Mokeded/Symm60HE/plate/Symm60HE-plate-universal-right.dxf

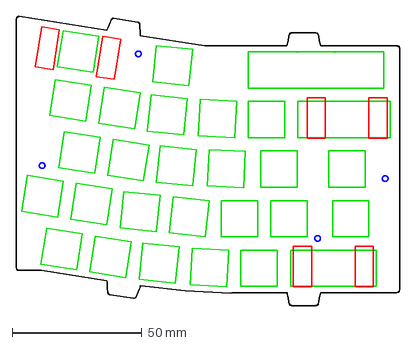
[picture p15: CAD file, 2026-10-05]
plate/Symm60HE-plate-universal-right.dxf
147.4 x 111.2 mm
