Mokeded/Symm60HE/case/fusion360/models/official/CCTC_TCC0603X5R106M6R3CT_C380318.step

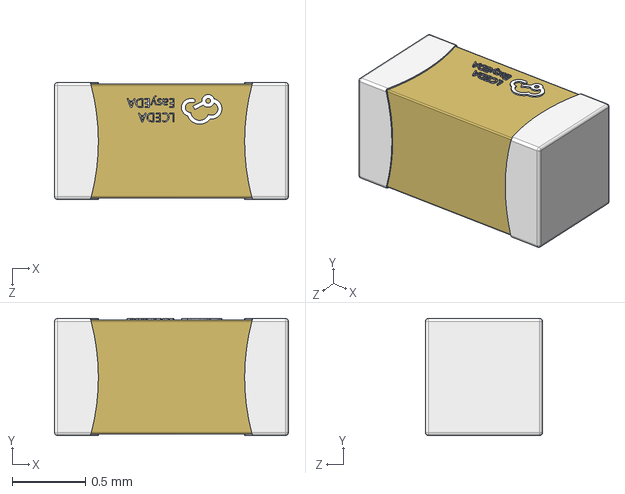
[picture p16: CAD file, 2026-10-05]
case/fusion360/models/official/CCTC_TCC0603X5R106M6R3CT_C380318.step
1.60 x 0.8 x 0.8 mm
