Mokeded/Symm60HE/case/fusion360/Symm60HE-RightPlate.step

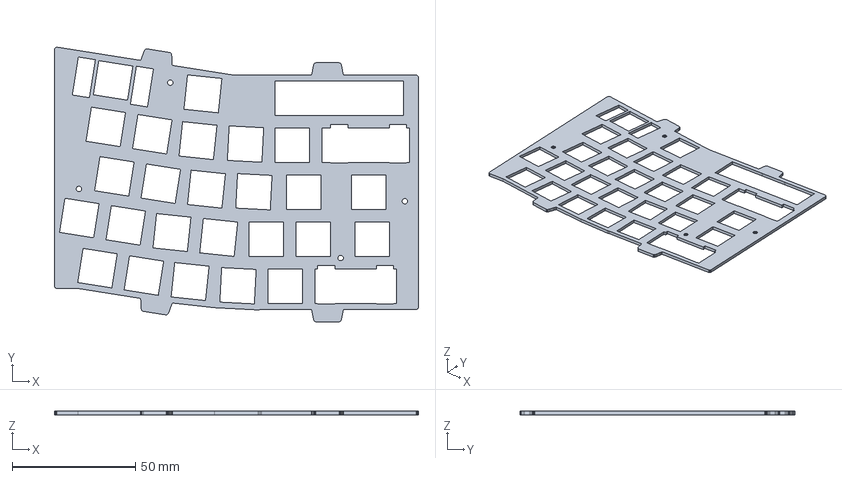
[picture p17: CAD file, 2026-10-05]
case/fusion360/Symm60HE-RightPlate.step
147.4 x 111.2 x 1.50 mm
