Mokeded/Symm60HE/plate/Symm60HE-plate-wkl-left-arrows-right-bs2-left.dxf

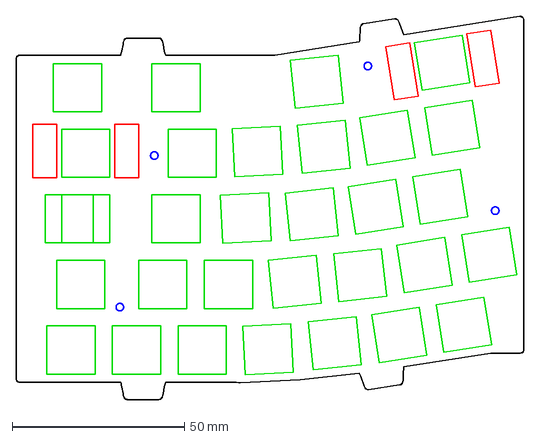
[picture p18: CAD file, 2026-10-05]
plate/Symm60HE-plate-wkl-left-arrows-right-bs2-left.dxf
147.4 x 111.2 mm
