Mokeded/Symm60HE/case/fusion360/models/official/TI_SN74AHCT1G125DBVR_C7484.step

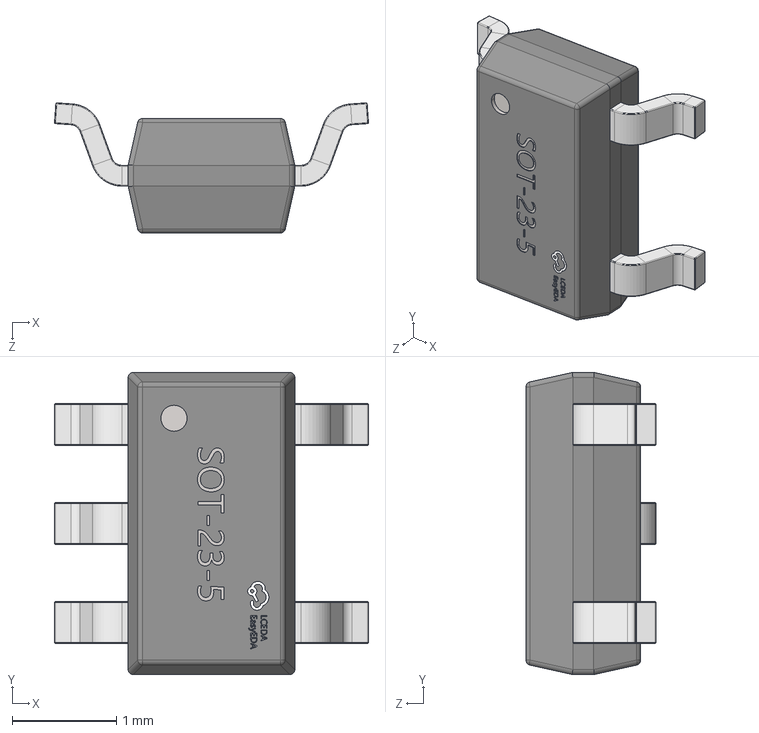
[picture p19: CAD file, 2026-10-05]
case/fusion360/models/official/TI_SN74AHCT1G125DBVR_C7484.step
3.01 x 2.90 x 1.25 mm
