Mokeded/Symm60HE/case/fusion360/Symm60HE-LeftRibbonCable.step

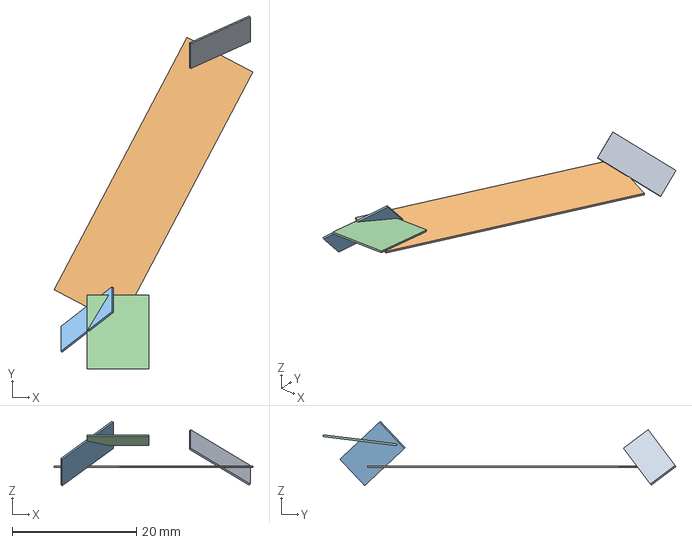
[picture p20: CAD file, 2026-10-05]
case/fusion360/Symm60HE-LeftRibbonCable.step
32.0 x 56.8 x 10.4 mm
