Mokeded/Symm60HE/case/fusion360/models/official/OPSCO_SK6812MINI-E_C5149201.step

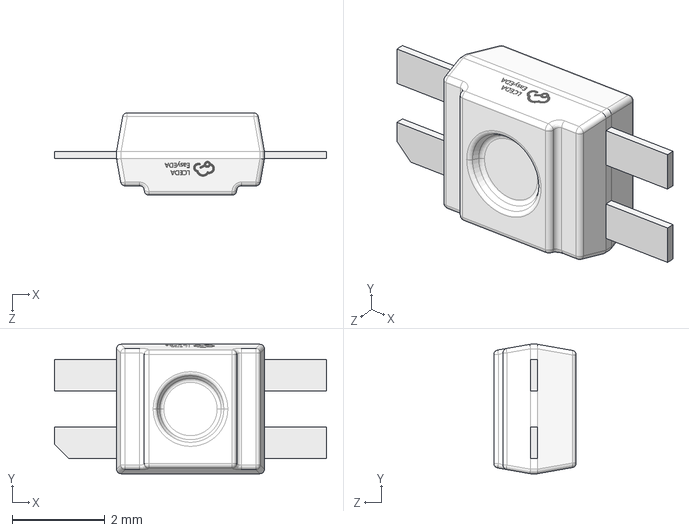
[picture p22: CAD file, 2026-10-05]
case/fusion360/models/official/OPSCO_SK6812MINI-E_C5149201.step
5.88 x 2.80 x 1.78 mm
