Mokeded/Symm60HE/case/fusion360/Symm60HE-LeftPlate.step

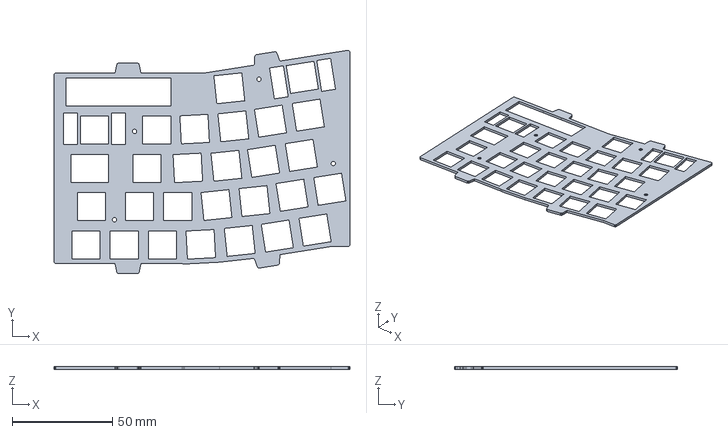
[picture p23: CAD file, 2026-10-05]
case/fusion360/Symm60HE-LeftPlate.step
147.4 x 111.2 x 1.50 mm
