Mokeded/Symm60HE/plate/Symm60HE-gasket-pads-wklarrows.dxf

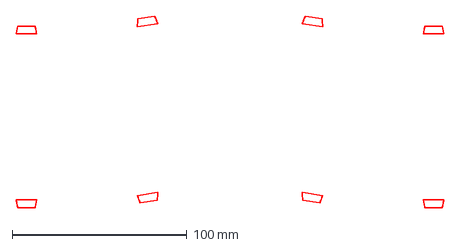
[picture p24: CAD file, 2026-10-05]
plate/Symm60HE-gasket-pads-wklarrows.dxf
244.8 x 109.5 mm
