Mokeded/Symm60HE/case/fusion360/models/official/ARTERY_AT32F405RCT7_C47090415.step

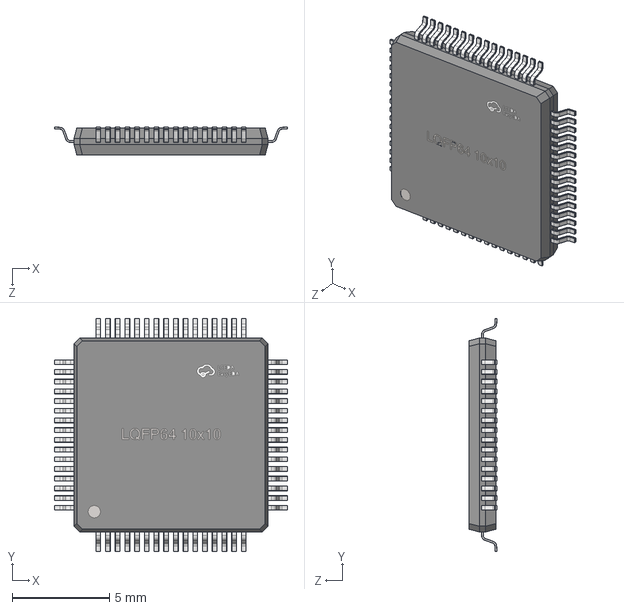
[picture p25: CAD file, 2026-10-05]
case/fusion360/models/official/ARTERY_AT32F405RCT7_C47090415.step
12.0 x 12.0 x 1.45 mm
