Mokeded/Symm60HE/plate/Symm60HE-gasket-pads-three-key-left-wkl-right.dxf

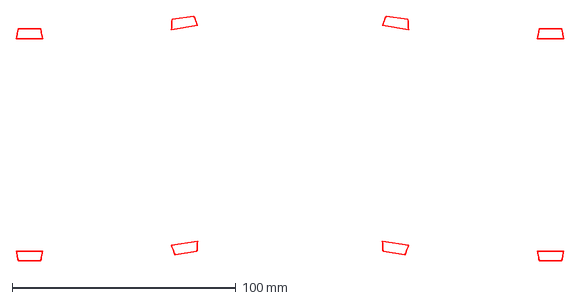
[picture p26: CAD file, 2026-10-05]
plate/Symm60HE-gasket-pads-three-key-left-wkl-right.dxf
244.8 x 109.5 mm
