Mokeded/Symm60HE/case/fusion360/models/official/UNI-ROYAL_0402WGF1202TCE_C25752.step

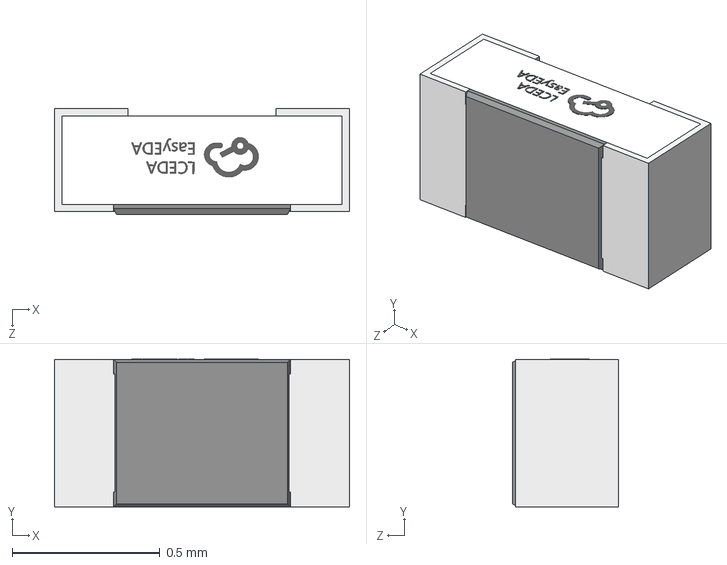
[picture p27: CAD file, 2026-10-05]
case/fusion360/models/official/UNI-ROYAL_0402WGF1202TCE_C25752.step
1.00 x 0.501 x 0.36 mm
