Mokeded/Symm60HE/case/fusion360/Symm60HE-RightSwitches.step

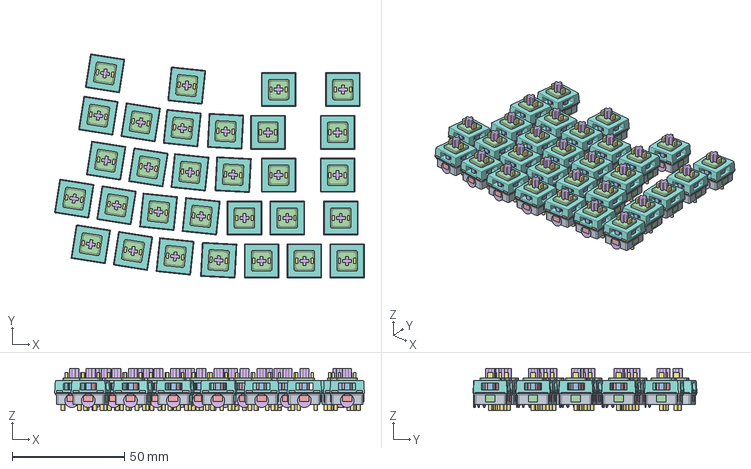
[picture p28: CAD file, 2026-10-05]
case/fusion360/Symm60HE-RightSwitches.step
137.9 x 99.8 x 18.8 mm
