Mokeded/Symm60HE/case/fusion360/models/official/TI_SN74LV4051APWR_C7793.step

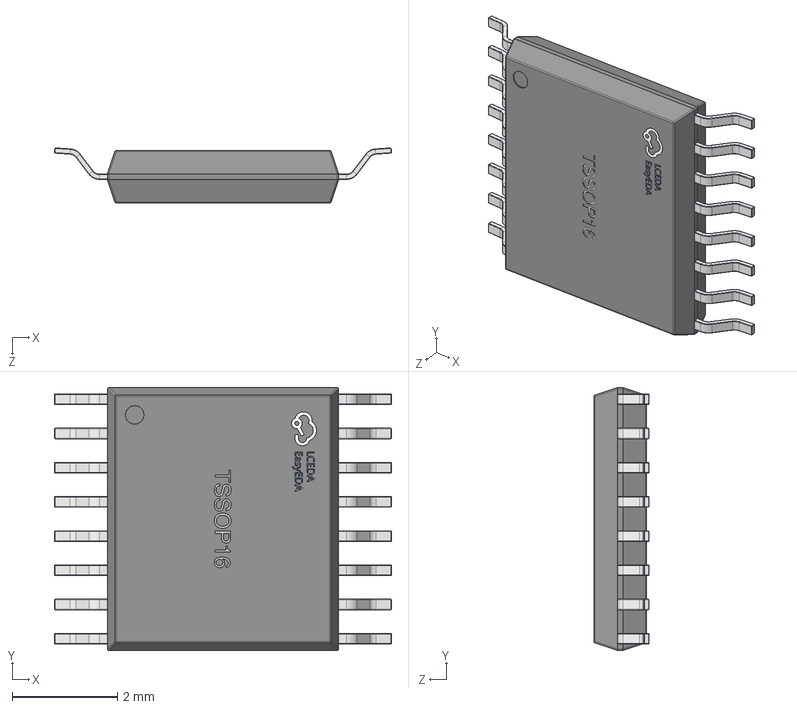
[picture p30: CAD file, 2026-10-05]
case/fusion360/models/official/TI_SN74LV4051APWR_C7793.step
6.41 x 5.00 x 1.05 mm
