Mokeded/Symm60HE/case/fusion360/Symm60HE-RightRibbonCable.step

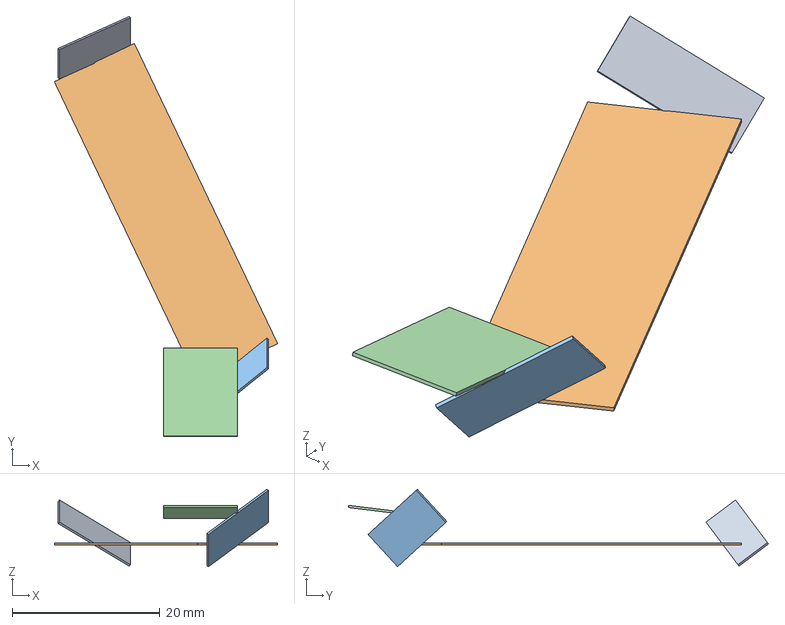
[picture p31: CAD file, 2026-10-05]
case/fusion360/Symm60HE-RightRibbonCable.step
30.2 x 56.8 x 10.5 mm
