Mokeded/Symm60HE/case/fusion360/models/official/YXC_X322512MSB4SI_C9002.step

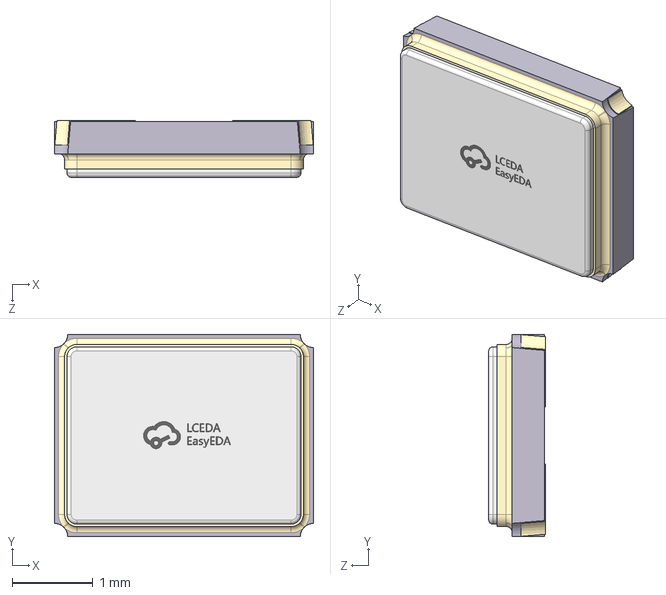
[picture p33: CAD file, 2026-10-05]
case/fusion360/models/official/YXC_X322512MSB4SI_C9002.step
3.20 x 2.50 x 0.701 mm
