Mokeded/Symm60HE/plate/Symm60HE-plate-wklbs2-left.dxf

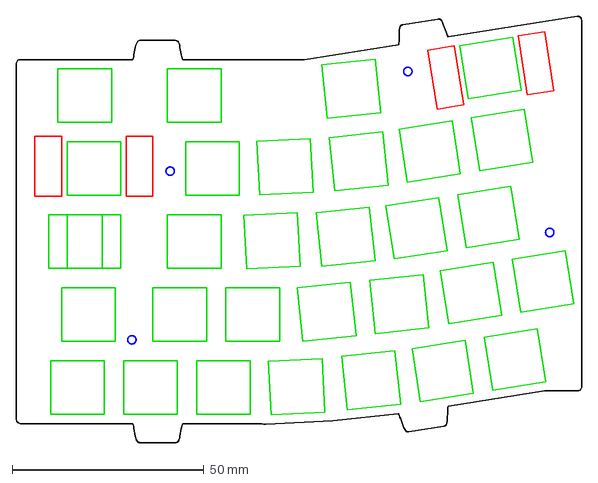
[picture p34: CAD file, 2026-10-05]
plate/Symm60HE-plate-wklbs2-left.dxf
147.4 x 111.2 mm
