Mokeded/Symm60HE/case/fusion360/models/official/NOVOSENSE_MT9102ET_C5447698.step

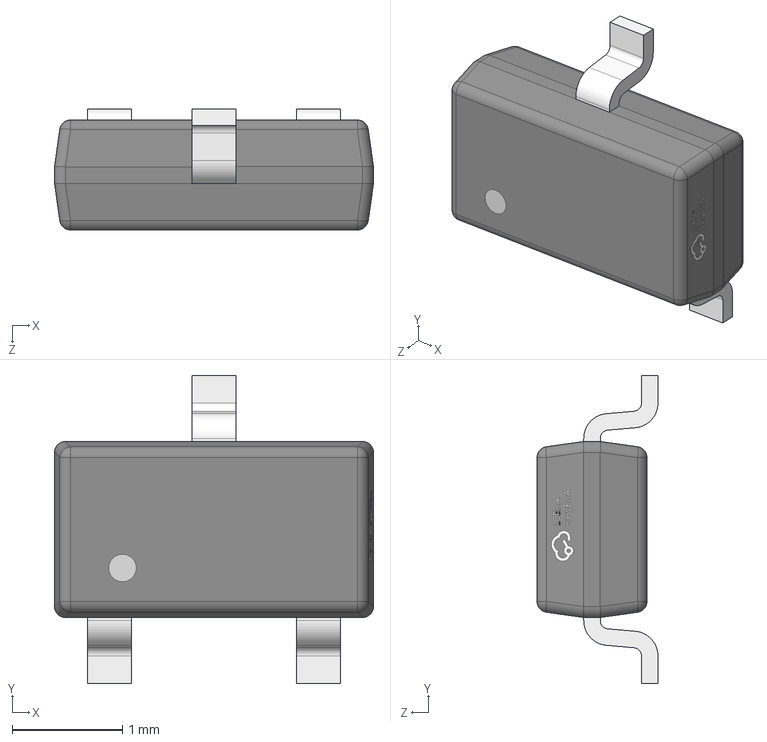
[picture p35: CAD file, 2026-10-05]
case/fusion360/models/official/NOVOSENSE_MT9102ET_C5447698.step
2.90 x 2.80 x 1.10 mm
