Mokeded/Symm60HE/case/fusion360/models/official/XKB_TS-1187A-B-A-B_C318884.stp

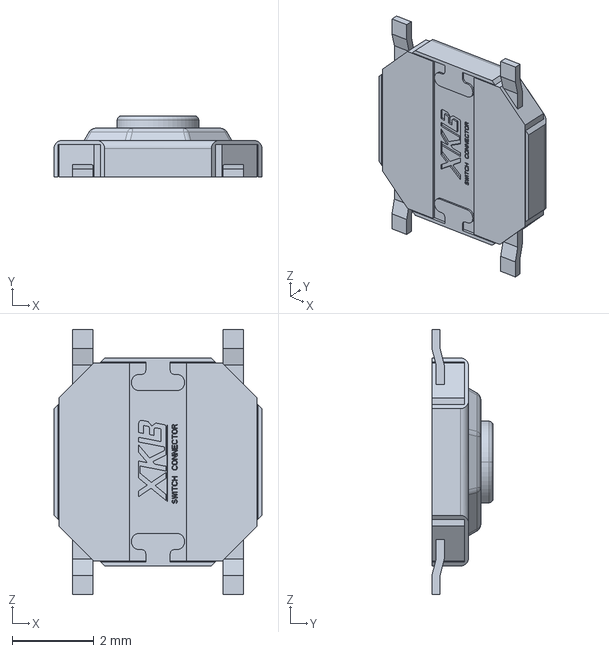
[picture p37: CAD file, 2026-09-21]
case/fusion360/models/official/XKB_TS-1187A-B-A-B_C318884.stp
5.10 x 1.50 x 6.50 mm
