Mokeded/Symm60HE/plate/Symm60HE-plate-wklarrows-left.dxf

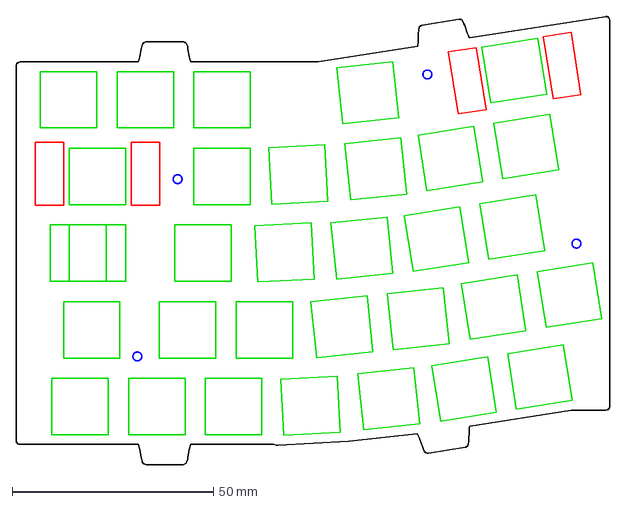
[picture p38: CAD file, 2026-10-05]
plate/Symm60HE-plate-wklarrows-left.dxf
147.4 x 111.2 mm
