Mokeded/Symm60HE/case/fusion360/models/official/BOOMELE_1.0-12P_C20111.step

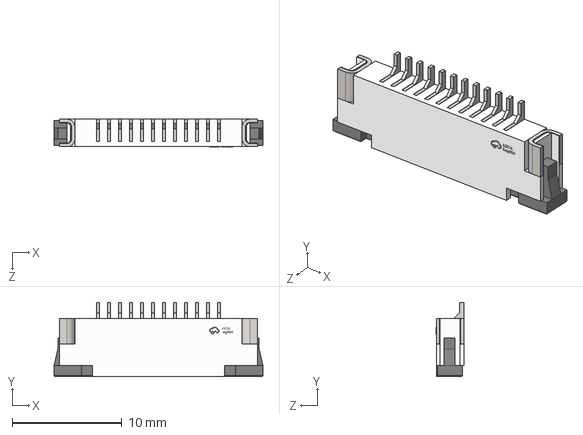
[picture p39: CAD file, 2026-09-13]
case/fusion360/models/official/BOOMELE_1.0-12P_C20111.step
19.0 x 6.75 x 2.51 mm
