Mokeded/Symm60HE/case/fusion360/Symm60HE-DaughterboardPCBComponents.step

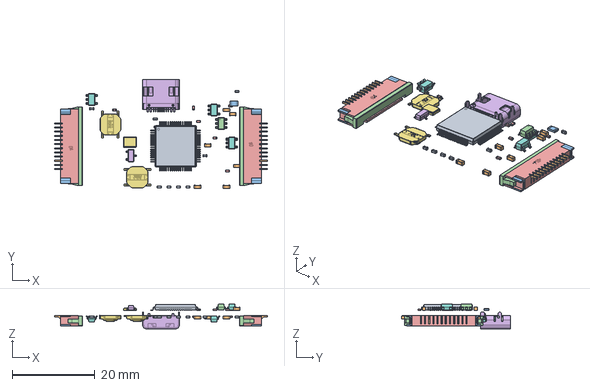
[picture p40: CAD file, 2026-09-21]
case/fusion360/Symm60HE-DaughterboardPCBComponents.step
51.3 x 26.3 x 6.00 mm
