Mokeded/Symm60HE/case/fusion360/models/official/HRO_TYPE-C-31-M-12_C165948.step

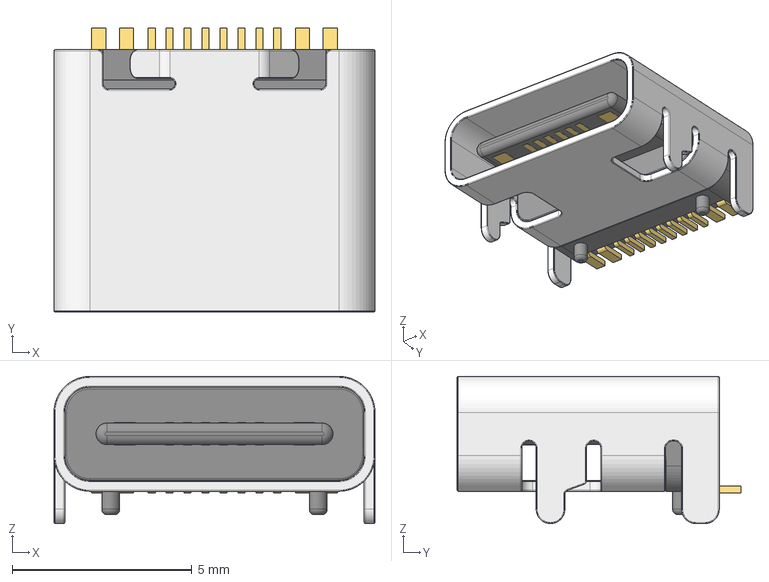
[picture p42: CAD file, 2026-09-13]
case/fusion360/models/official/HRO_TYPE-C-31-M-12_C165948.step
8.94 x 7.90 x 4.10 mm
