Mokeded/Symm60HE/plate/Symm60HE-plate-wklarrows-right.dxf

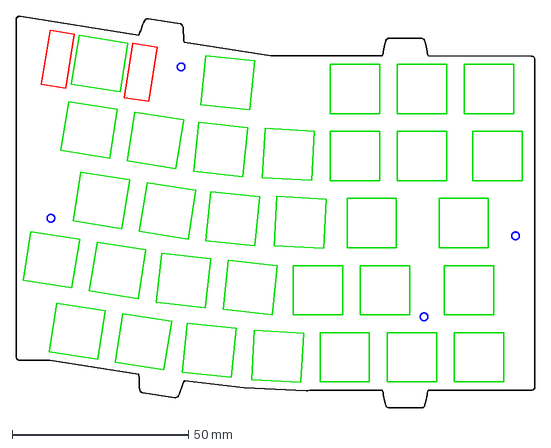
[picture p44: CAD file, 2026-10-05]
plate/Symm60HE-plate-wklarrows-right.dxf
147.4 x 111.2 mm
