Mokeded/Symm60HE/plate/Symm60HE-gasket-pads-universal.dxf

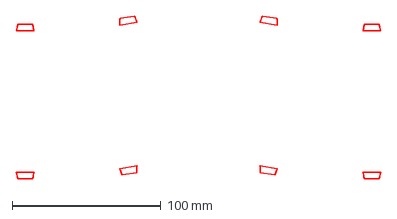
[picture p45: CAD file, 2026-10-05]
plate/Symm60HE-gasket-pads-universal.dxf
244.8 x 109.5 mm
