Mokeded/Symm60HE/plate/Symm60HE-plate-universal-left.dxf

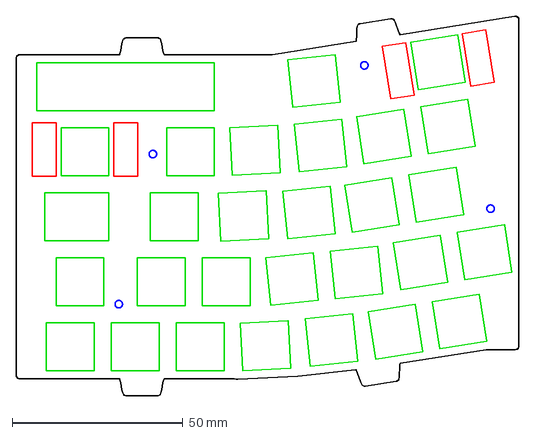
[picture p46: CAD file, 2026-10-05]
plate/Symm60HE-plate-universal-left.dxf
147.4 x 111.2 mm
