Mokeded/Symm60HE/plate/Symm60HE-gasket-pads-wklbs2.dxf

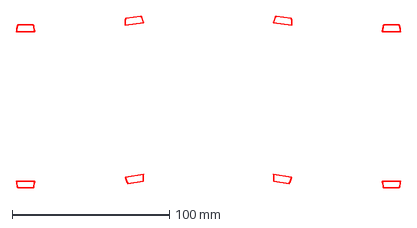
[picture p47: CAD file, 2026-10-05]
plate/Symm60HE-gasket-pads-wklbs2.dxf
244.8 x 109.5 mm
