Mokeded/Symm60HE/plate/Symm60HE-plate-wkl-left-arrows-right-right.dxf

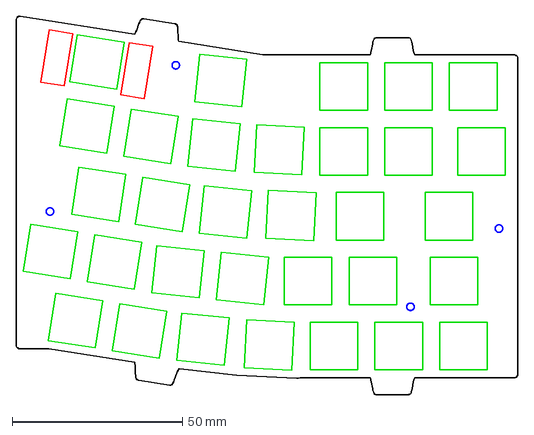
[picture p48: CAD file, 2026-10-05]
plate/Symm60HE-plate-wkl-left-arrows-right-right.dxf
147.4 x 111.2 mm
