Mokeded/Symm60HE/plate/Symm60HE-gasket-pads-wkl-left-arrows-right.dxf

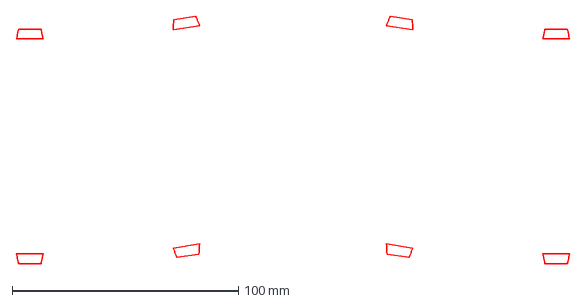
[picture p49: CAD file, 2026-10-05]
plate/Symm60HE-gasket-pads-wkl-left-arrows-right.dxf
244.8 x 109.5 mm
