Mokeded/Symm60HE/plate/Symm60HE-plate-wklbs2arrows-right.dxf

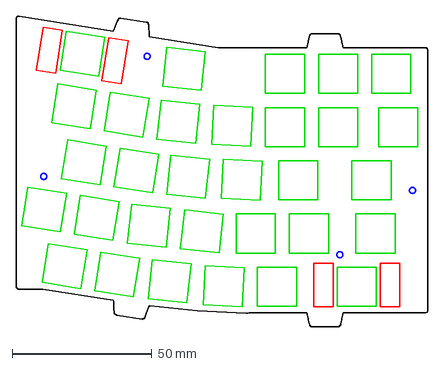
[picture p50: CAD file, 2026-10-05]
plate/Symm60HE-plate-wklbs2arrows-right.dxf
147.4 x 111.2 mm
