Mokeded/Symm60HE/plate/Symm60HE-plate-wkl-left-arrows-right-left.dxf

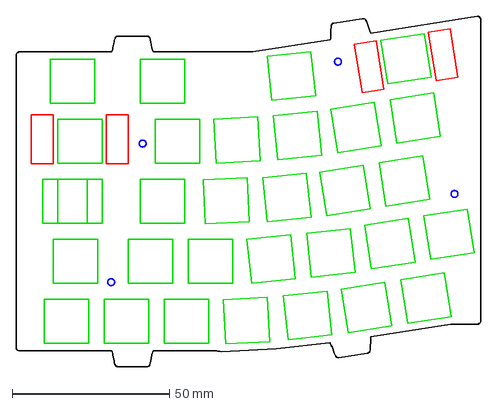
[picture p51: CAD file, 2026-10-05]
plate/Symm60HE-plate-wkl-left-arrows-right-left.dxf
147.4 x 111.2 mm
