Mokeded/Symm60HE/plate/Symm60HE-plate-three-key-left-wkl-right-left.dxf

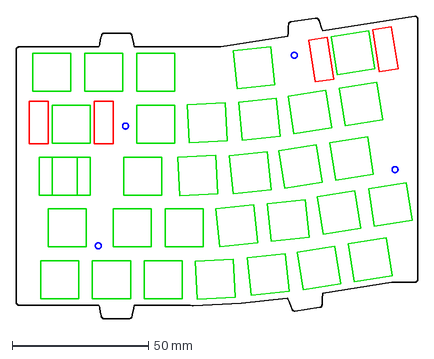
[picture p52: CAD file, 2026-10-05]
plate/Symm60HE-plate-three-key-left-wkl-right-left.dxf
147.4 x 111.2 mm
