Mokeded/Symm60HE/plate/Symm60HE-plate-wklbs2-right.dxf

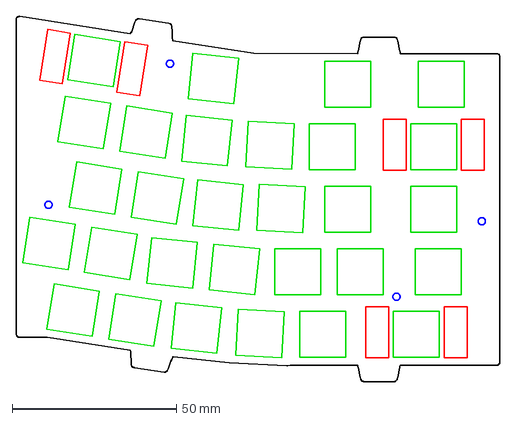
[picture p54: CAD file, 2026-10-05]
plate/Symm60HE-plate-wklbs2-right.dxf
147.4 x 111.2 mm
