Mokeded/Symm60HE/plate/Symm60HE-gasket-pads-wkl-left-arrows-right-bs2.dxf

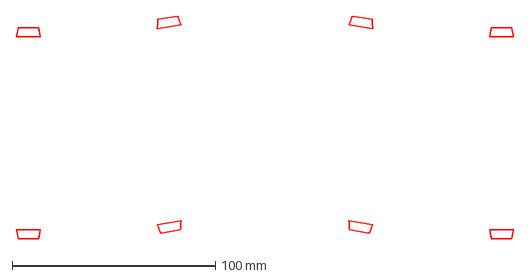
[picture p55: CAD file, 2026-10-05]
plate/Symm60HE-gasket-pads-wkl-left-arrows-right-bs2.dxf
244.8 x 109.5 mm
