Mokeded/Symm60HE/plate/Symm60HE-plate-wkl-right.dxf

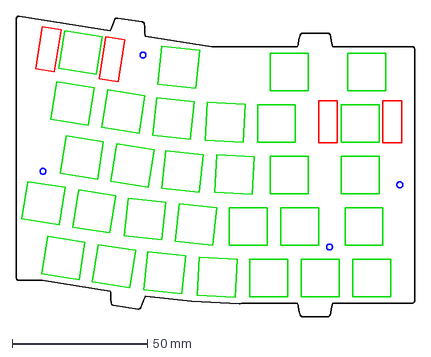
[picture p56: CAD file, 2026-10-05]
plate/Symm60HE-plate-wkl-right.dxf
147.4 x 111.2 mm
