Mokeded/Symm60HE/plate/DOE60-plate-wklbs2arrows.dxf

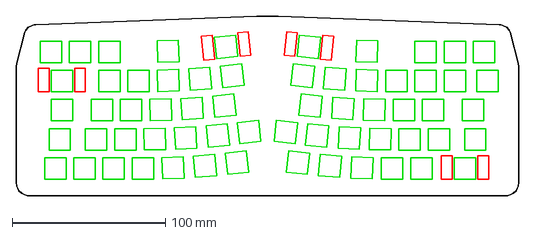
[picture p57: CAD file, 2026-09-10]
plate/DOE60-plate-wklbs2arrows.dxf
328.0 x 117.2 mm
