Mokeded/Symm60HE/plate/DOE60-plate-wklbs2.dxf

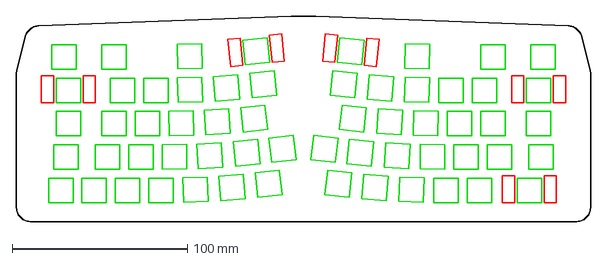
[picture p58: CAD file, 2026-09-10]
plate/DOE60-plate-wklbs2.dxf
328.0 x 117.2 mm
