Mokeded/Symm60HE/plate/DOE60-plate-universal.dxf

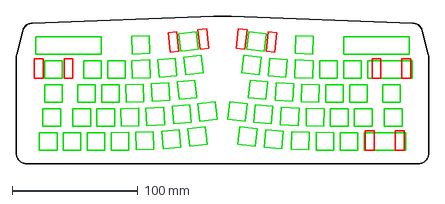
[picture p59: CAD file, 2026-09-10]
plate/DOE60-plate-universal.dxf
328.0 x 117.2 mm
