Mokeded/Symm60HE/plate/DOE60-plate-wkl.dxf

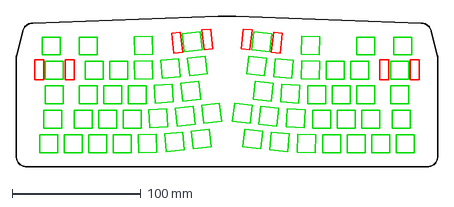
[picture p60: CAD file, 2026-09-10]
plate/DOE60-plate-wkl.dxf
328.0 x 117.2 mm
