Mokeded/Symm60HE/plate/DOE60-plate-wklarrows.dxf

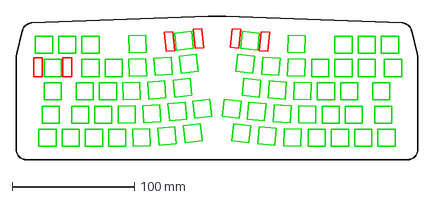
[picture p61: CAD file, 2026-09-10]
plate/DOE60-plate-wklarrows.dxf
328.0 x 117.2 mm
