Mokeded/Symm60HE/firmware/libhmk/src/migration.c

/*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
 * You should have received a copy of the GNU General Public License along with
 * this program. If not, see <https://www.gnu.org/licenses/>.
 */

#include "migration.h"

#include "eeconfig.h"
#include "wear_leveling.h"

#define MIGRATION_V1_0_GLOBAL_CONFIG_SIZE 12
#define MIGRATION_V1_0_ADVANCED_KEY_SIZE 12
#define MIGRATION_V1_0_PROFILE_CONFIG_SIZE                                     \
  (NUM_LAYERS * NUM_KEYS + NUM_KEYS * 4 +                                      \
   NUM_ADVANCED_KEYS * MIGRATION_V1_0_ADVANCED_KEY_SIZE + 1)

static bool v1_1_global_config_func(uint8_t *dst, const uint8_t *src);
static bool v1_1_profile_config_func(uint8_t profile, uint8_t *dst,
                                     const uint8_t *src);

#define MIGRATION_V1_1_GLOBAL_CONFIG_SIZE 14
#define MIGRATION_V1_1_PROFILE_CONFIG_SIZE                                     \
  (NUM_LAYERS * NUM_KEYS + NUM_KEYS * 4 +                                      \
   NUM_ADVANCED_KEYS * MIGRATION_V1_0_ADVANCED_KEY_SIZE + NUM_KEYS + 9 + 1)

static bool v1_2_global_config_func(uint8_t *dst, const uint8_t *src);
static bool v1_2_profile_config_func(uint8_t profile, uint8_t *dst,
                                     const uint8_t *src);

#define MIGRATION_V1_2_GLOBAL_CONFIG_SIZE (14 + NUM_KEYS * 2)
#define MIGRATION_V1_2_PROFILE_CONFIG_SIZE MIGRATION_V1_1_PROFILE_CONFIG_SIZE

static bool v1_3_global_config_func(uint8_t *dst, const uint8_t *src);
static bool v1_3_profile_config_func(uint8_t profile, uint8_t *dst,
                                     const uint8_t *src);

#define MIGRATION_V1_3_GLOBAL_CONFIG_SIZE MIGRATION_V1_2_GLOBAL_CONFIG_SIZE
#define MIGRATION_V1_3_PROFILE_CONFIG_SIZE MIGRATION_V1_2_PROFILE_CONFIG_SIZE

static bool v1_4_global_config_func(uint8_t *dst, const uint8_t *src);
static bool v1_4_profile_config_func(uint8_t profile, uint8_t *dst,
                                     const uint8_t *src);

#define MIGRATION_V1_4_GLOBAL_CONFIG_SIZE MIGRATION_V1_3_GLOBAL_CONFIG_SIZE
#define MIGRATION_V1_4_PROFILE_CONFIG_SIZE MIGRATION_V1_3_PROFILE_CONFIG_SIZE

static bool v1_5_global_config_func(uint8_t *dst, const uint8_t *src);
static bool v1_5_profile_config_func(uint8_t profile, uint8_t *dst,
                                     const uint8_t *src);

#define MIGRATION_V1_5_GLOBAL_CONFIG_SIZE MIGRATION_V1_4_GLOBAL_CONFIG_SIZE
#define MIGRATION_V1_5_ADVANCED_KEY_SIZE                                       \
  (3 + 2 * NUM_DYNAMIC_KEYSTROKE_MAX_BINDINGS + 1)
#define MIGRATION_V1_5_MACRO_NODE_SIZE 4
#define MIGRATION_V1_5_MACRO_NODE_NONE UINT8_MAX
#define MIGRATION_V1_5_PROFILE_CONFIG_SIZE                                     \
  (NUM_LAYERS * NUM_KEYS + NUM_KEYS * 4 +                                      \
   NUM_ADVANCED_KEYS * MIGRATION_V1_5_ADVANCED_KEY_SIZE +                      \
   NUM_MACRO_NODES * MIGRATION_V1_5_MACRO_NODE_SIZE + NUM_KEYS + 9 + 1)

#if defined(RGB_ENABLE)
static bool v1_6_global_config_func(uint8_t *dst, const uint8_t *src);
static bool v1_6_profile_config_func(uint8_t profile, uint8_t *dst,
                                     const uint8_t *src);

#define MIGRATION_V1_6_GLOBAL_CONFIG_SIZE                                      \
  (MIGRATION_V1_5_GLOBAL_CONFIG_SIZE + sizeof(rgb_config_t))
#define MIGRATION_V1_6_PROFILE_CONFIG_SIZE MIGRATION_V1_5_PROFILE_CONFIG_SIZE
#endif

// Migration metadata for each configuration version. The first entry is
// reserved for the initial version (v1.0) which does not require migration.
static const migration_t migrations[] = {
    {
        .version = 0x0100,
        .global_config_size = MIGRATION_V1_0_GLOBAL_CONFIG_SIZE,
        .profile_config_size = MIGRATION_V1_0_PROFILE_CONFIG_SIZE,
    },
    {
        .version = 0x0101,
        .global_config_size = MIGRATION_V1_1_GLOBAL_CONFIG_SIZE,
        .profile_config_size = MIGRATION_V1_1_PROFILE_CONFIG_SIZE,
        .global_config_func = v1_1_global_config_func,
        .profile_config_func = v1_1_profile_config_func,
    },
    {
        .version = 0x0102,
        .global_config_size = MIGRATION_V1_2_GLOBAL_CONFIG_SIZE,
        .profile_config_size = MIGRATION_V1_2_PROFILE_CONFIG_SIZE,
        .global_config_func = v1_2_global_config_func,
        .profile_config_func = v1_2_profile_config_func,
    },
    {
        .version = 0x0103,
        .global_config_size = MIGRATION_V1_3_GLOBAL_CONFIG_SIZE,
        .profile_config_size = MIGRATION_V1_3_PROFILE_CONFIG_SIZE,
        .global_config_func = v1_3_global_config_func,
        .profile_config_func = v1_3_profile_config_func,
    },
    {
        .version = 0x0104,
        .global_config_size = MIGRATION_V1_4_GLOBAL_CONFIG_SIZE,
        .profile_config_size = MIGRATION_V1_4_PROFILE_CONFIG_SIZE,
        .global_config_func = v1_4_global_config_func,
        .profile_config_func = v1_4_profile_config_func,
    },
    {
        .version = 0x0105,
        .global_config_size = MIGRATION_V1_5_GLOBAL_CONFIG_SIZE,
        .profile_config_size = MIGRATION_V1_5_PROFILE_CONFIG_SIZE,
        .global_config_func = v1_5_global_config_func,
        .profile_config_func = v1_5_profile_config_func,
    },
#if defined(RGB_ENABLE)
    {
        .version = 0x0106,
        .global_config_size = MIGRATION_V1_6_GLOBAL_CONFIG_SIZE,
        .profile_config_size = MIGRATION_V1_6_PROFILE_CONFIG_SIZE,
        .global_config_func = v1_6_global_config_func,
        .profile_config_func = v1_6_profile_config_func,
    },
#endif
};

// An assertion to remind us to bump the persistent configuration version, and
// implement a migration function if there is a change to the configuration
// type. Update the assertion when a new version is added.
#if defined(RGB_ENABLE)
_Static_assert(MIGRATION_V1_6_GLOBAL_CONFIG_SIZE +
                       NUM_PROFILES * MIGRATION_V1_6_PROFILE_CONFIG_SIZE ==
                   offsetof(eeconfig_t, magic_end),
               "Invalid RGB configuration size");
#else
_Static_assert(MIGRATION_V1_5_GLOBAL_CONFIG_SIZE +
                       NUM_PROFILES * MIGRATION_V1_5_PROFILE_CONFIG_SIZE ==
                   offsetof(eeconfig_t, magic_end),
               "Invalid configuration size");
#endif

// An assertion to remind us if there is a breaking change to `MACRO_NODE_NONE`.
// Update the assertion when a new version is added.
_Static_assert(MIGRATION_V1_5_MACRO_NODE_NONE == MACRO_NODE_NONE,
               "Invalid MACRO_NODE_NONE");

bool migration_try_migrate(void) {
  if (eeconfig->magic_start != EECONFIG_MAGIC_START)
    // The magic start is always the same for any version.
    return false;

  const uint16_t config_version = eeconfig->version;
  // We alternate between two buffers to save the memory.
  uint8_t current_buf = 0;
  uint8_t bufs[2][sizeof(eeconfig_t)];

  // Let `bufs[0]` be the current configuration.
  memcpy(bufs[0], eeconfig, sizeof(eeconfig_t));
  // Skip v1.0 migration since it is the initial version
  for (uint32_t i = 1; i < M_ARRAY_SIZE(migrations); i++) {
    const migration_t *m = &migrations[i];
    const migration_t *prev_m = &migrations[i - 1];

    if (m->version <= config_version)
      // Skip migrations that are not applicable
      continue;

    const uint8_t *src = bufs[current_buf];
    uint8_t *dst = bufs[current_buf ^ 1];

    if (m->global_config_func && !m->global_config_func(dst, src))
      // Migration failed for the global configuration
      return false;

    if (m->profile_config_func) {
      for (uint8_t p = 0; p < NUM_PROFILES; p++) {
        // Move the pointers to the start of each profile configuration
        const uint8_t *profile_src =
            src + prev_m->global_config_size + p * prev_m->profile_config_size;
        uint8_t *profile_dst =
            dst + m->global_config_size + p * m->profile_config_size;

        if (!m->profile_config_func(p, profile_dst, profile_src))
          // Migration failed for the profile configuration
          return false;
      }
    }

    // Update the version in the destination buffer
    ((eeconfig_t *)dst)->version = m->version;
    // Switch to the next buffer for the next migration
    current_buf ^= 1;
  }

  // Make sure the configuration is valid after migration
  ((eeconfig_t *)bufs[current_buf])->magic_end = EECONFIG_MAGIC_END;
  // We reflect the update in the flash.
  return wear_leveling_write(0, &bufs[current_buf], sizeof(eeconfig_t));
}

//--------------------------------------------------------------------+
// Helper Functions
//--------------------------------------------------------------------+

static void migration_memcpy(uint8_t **dst, const uint8_t **src, uint32_t len) {
  memcpy(*dst, *src, len);
  *dst += len;
  *src += len;
}

static void migration_memset(uint8_t **dst, uint8_t value, uint32_t len) {
  memset(*dst, value, len);
  *dst += len;
}

#define MAKE_MIGRATION_ASSIGN(type)                                            \
  static void migration_assign_##type(uint8_t **dst, type value) {             \
    *(type *)(*dst) = value;                                                   \
    *dst = (uint8_t *)((type *)(*dst) + 1);                                    \
  }

MAKE_MIGRATION_ASSIGN(uint8_t)
MAKE_MIGRATION_ASSIGN(uint16_t)

//--------------------------------------------------------------------+
// v1.0 -> v1.1 Migration
//--------------------------------------------------------------------+

bool v1_1_global_config_func(uint8_t *dst, const uint8_t *src) {
  if (((eeconfig_t *)src)->version != 0x0100)
    // Expected version v1.0
    return false;

  // Copy `magic_start` to `calibration`
  migration_memcpy(&dst, &src, 10);
  // Default `options` to 0
  migration_assign_uint16_t(&dst, 0);
  // Copy `current_profile` and `last_non_default_profile`
  migration_memcpy(&dst, &src, 2);

  return true;
}

bool v1_1_profile_config_func(uint8_t profile, uint8_t *dst,
                              const uint8_t *src) {
  // Save the `keymap` offset
  uint8_t *keymap = dst;
  // Copy `keymap` to `actuation_map`
  migration_memcpy(&dst, &src, (NUM_LAYERS * NUM_KEYS) + (NUM_KEYS * 4));
  // Update keycodes to include `KC_INT1` ... `KC_LNG6`
  for (uint32_t i = 0; i < NUM_LAYERS * NUM_KEYS; i++) {
    if (0x70 <= keymap[i] && keymap[i] <= 0x71)
      // `KC_LNG1` and `KC_LNG2`
      keymap[i] += 0x06;
    else if (0x72 <= keymap[i] && keymap[i] <= 0x96)
      // `KC_LEFT_CTRL` ... `SP_MOUSE_BUTTON_5`
      keymap[i] += 0x09;
  }
  // Save the `advanced_keys` offset
  uint8_t *advanced_keys = dst;
  // Copy `advanced_keys`
  migration_memcpy(&dst, &src,
                   NUM_ADVANCED_KEYS * MIGRATION_V1_0_ADVANCED_KEY_SIZE);
  // Default `hold_on_other_key_press` to 0
  for (uint8_t i = 0; i < NUM_ADVANCED_KEYS; i++) {
    uint8_t *ak = advanced_keys + i * MIGRATION_V1_0_ADVANCED_KEY_SIZE;
    if (ak[2] == AK_TYPE_TAP_HOLD)
      ak[7] = 0;
  }
  // Set `gamepad_buttons` to 0
  migration_memset(&dst, 0, NUM_KEYS);
  // Default `analog_curve` to linear
  migration_assign_uint8_t(&dst, 4), migration_assign_uint8_t(&dst, 20);
  migration_assign_uint8_t(&dst, 85), migration_assign_uint8_t(&dst, 95);
  migration_assign_uint8_t(&dst, 165), migration_assign_uint8_t(&dst, 170);
  migration_assign_uint8_t(&dst, 255), migration_assign_uint8_t(&dst, 255);
  // Default `keyboard_enabled` and `snappy_joystick` to true
  migration_assign_uint8_t(&dst, 0b00001001);
  // Copy `tick_rate`
  migration_memcpy(&dst, &src, 1);

  return true;
}

//--------------------------------------------------------------------+
// v1.1 -> v1.2 Migration
//--------------------------------------------------------------------+

bool v1_2_global_config_func(uint8_t *dst, const uint8_t *src) {
  if (((eeconfig_t *)src)->version != 0x0101)
    // Expected version v1.1
    return false;

  // Copy `magic_start` to `calibration`
  migration_memcpy(&dst, &src, 10);
  // Set `bottom_out_threshold` to 0
  migration_memset(&dst, 0, NUM_KEYS * 2);
  // Copy `options` to `last_non_default_profile`
  migration_memcpy(&dst, &src, 4);

  return true;
}

bool v1_2_profile_config_func(uint8_t profile, uint8_t *dst,
                              const uint8_t *src) {
  // Copy the entire profile
  migration_memcpy(&dst, &src, MIGRATION_V1_2_PROFILE_CONFIG_SIZE);

  return true;
}

//--------------------------------------------------------------------+
// v1.2 -> v1.3 Migration
//--------------------------------------------------------------------+

bool v1_3_global_config_func(uint8_t *dst, const uint8_t *src) {
  if (((eeconfig_t *)src)->version != 0x0102)
    // Expected version v1.2
    return false;

  // Copy `magic_start` to `bottom_out_threshold`
  migration_memcpy(&dst, &src, 10 + NUM_KEYS * 2);
  // Default `save_bottom_out_threshold` to true
  uint16_t options = *((uint16_t *)src) | (1 << 1);
  migration_assign_uint16_t(&dst, options);
  src += sizeof(options);
  // Copy `current_profile` to `last_non_default_profile`
  migration_memcpy(&dst, &src, 2);

  return true;
}

bool v1_3_profile_config_func(uint8_t profile, uint8_t *dst,
                              const uint8_t *src) {
  // Copy the entire profile
  migration_memcpy(&dst, &src, MIGRATION_V1_3_PROFILE_CONFIG_SIZE);

  return true;
}

//--------------------------------------------------------------------+
// v1.3 -> v1.4 Migration
//--------------------------------------------------------------------+

bool v1_4_global_config_func(uint8_t *dst, const uint8_t *src) {
  if (((eeconfig_t *)src)->version != 0x0103)
    // Expected version v1.3
    return false;

  // Copy `magic_start` to `bottom_out_threshold`
  migration_memcpy(&dst, &src, 10 + NUM_KEYS * 2);
  // Default `high_polling_rate_enabled` to true
  uint16_t options = *((uint16_t *)src) | (1 << 2);
  migration_assign_uint16_t(&dst, options);
  src += sizeof(options);
  // Copy `current_profile` to `last_non_default_profile`
  migration_memcpy(&dst, &src, 2);

  return true;
}

bool v1_4_profile_config_func(uint8_t profile, uint8_t *dst,
                              const uint8_t *src) {
  // Copy the entire profile
  migration_memcpy(&dst, &src, MIGRATION_V1_4_PROFILE_CONFIG_SIZE);

  return true;
}

//--------------------------------------------------------------------+
// v1.4 -> v1.5 Migration
//--------------------------------------------------------------------+

bool v1_5_global_config_func(uint8_t *dst, const uint8_t *src) {
  if (((eeconfig_t *)src)->version != 0x0104)
    // Expected version v1.4
    return false;

  // Copy the entire global configuration.
  migration_memcpy(&dst, &src, MIGRATION_V1_5_GLOBAL_CONFIG_SIZE);

  return true;
}

bool v1_5_profile_config_func(uint8_t profile, uint8_t *dst,
                              const uint8_t *src) {
  (void)profile;

  // Copy `keymap` to `actuation_map`.
  migration_memcpy(&dst, &src, NUM_LAYERS * NUM_KEYS + NUM_KEYS * 4);

  // Expand each advanced key record from 12 bytes to the current size and
  // clear the newly-added Dynamic Keystroke slots.
  for (uint8_t i = 0; i < NUM_ADVANCED_KEYS; i++) {
    migration_memcpy(&dst, &src, MIGRATION_V1_0_ADVANCED_KEY_SIZE);
    migration_memset(&dst, 0,
                     MIGRATION_V1_5_ADVANCED_KEY_SIZE -
                         MIGRATION_V1_0_ADVANCED_KEY_SIZE);
  }

  // Clear the new per-profile macro buffer.
  for (uint32_t i = 0; i < NUM_MACRO_NODES; i++) {
    migration_memset(&dst, 0, 3);
    migration_assign_uint8_t(&dst, MIGRATION_V1_5_MACRO_NODE_NONE);
  }

  // Copy the remaining profile fields.
  migration_memcpy(&dst, &src, NUM_KEYS + 9 + 1);

  return true;
}

#if defined(RGB_ENABLE)
//--------------------------------------------------------------------+
// v1.5 -> v1.6 Migration
//--------------------------------------------------------------------+

bool v1_6_global_config_func(uint8_t *dst, const uint8_t *src) {
  if (((eeconfig_t *)src)->version != 0x0105)
    return false;

  migration_memcpy(&dst, &src, MIGRATION_V1_5_GLOBAL_CONFIG_SIZE);
  const rgb_config_t default_rgb_config = DEFAULT_RGB_CONFIG;
  memcpy(dst, &default_rgb_config, sizeof(default_rgb_config));
  return true;
}

bool v1_6_profile_config_func(uint8_t profile, uint8_t *dst,
                              const uint8_t *src) {
  (void)profile;
  migration_memcpy(&dst, &src, MIGRATION_V1_6_PROFILE_CONFIG_SIZE);
  return true;
}
#endif
