Mokeded/Symm60HE/firmware/libhmk/src/layout.c

/*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
 * You should have received a copy of the GNU General Public License along with
 * this program. If not, see <https://www.gnu.org/licenses/>.
 */

#include "layout.h"

#include "advanced_keys.h"
#include "deferred_actions.h"
#include "eeconfig.h"
#include "hardware/hardware.h"
#include "hid.h"
#include "keycodes.h"
#include "lib/bitmap.h"
#include "matrix.h"
#include "xinput.h"

// Layer mask. Each bit represents whether a layer is active or not.
static uint16_t layer_mask;
static uint8_t default_layer;

/**
 * @brief Get the current layer
 *
 * The current layer is the highest layer that is currently active in the layer
 * mask. If no layers are active, the default layer is returned.
 *
 * @return Current layer
 */
__attribute__((always_inline)) static inline uint8_t
layout_get_current_layer(void) {
  return layer_mask ? 31 - __builtin_clz(layer_mask) : default_layer;
}

__attribute__((always_inline)) static inline void
layout_layer_on(uint8_t layer) {
  layer_mask |= (1 << layer);
}

__attribute__((always_inline)) static inline void
layout_layer_off(uint8_t layer) {
  layer_mask &= ~(1 << layer);
}

/**
 * @brief Lock the current layer
 *
 * This function sets the default layer to the current layer if it is not
 * already set. Otherwise, it sets the default layer to 0.
 *
 * @return None
 */
__attribute__((always_inline)) static inline void layout_layer_lock(void) {
  const uint8_t current_layer = layout_get_current_layer();
  default_layer = current_layer == default_layer ? 0 : current_layer;
}

/**
 * @brief Get the keycode of a key
 *
 * This function returns the keycode of a key in the current layer. If the key
 * is transparent, the function will search for the highest active layer with a
 * non-transparent keycode.
 *
 * @param current_layer Current layer
 * @param key Key index
 *
 * @return Keycode
 */
static uint8_t layout_get_keycode(uint8_t current_layer, uint8_t key) {
  // Find the first active layer with a non-transparent keycode
  for (uint32_t i = (uint32_t)current_layer + 1; i-- > 0;) {
    if (((layer_mask >> i) & 1) == 0)
      // Layer is not active
      continue;

    const uint8_t keycode = CURRENT_PROFILE.keymap[i][key];
    if (keycode != KC_TRANSPARENT)
      return keycode;
  }

  // No keycode found, use the default keycode
  return CURRENT_PROFILE.keymap[default_layer][key];
}

// Only send reports if they changed
static bool should_send_reports;
// Whether the key is disabled by `SP_KEY_LOCK`
static bitmap_t key_disabled[] = MAKE_BITMAP(NUM_KEYS);

// Track whether the key is currently pressed. Used to detect key events.
static bitmap_t key_press_states[] = MAKE_BITMAP(NUM_KEYS);
// Store the keycodes of the currently pressed keys. Layer/profile may change so
// we need to remember the keycodes we pressed to release them correctly.
static uint8_t active_keycodes[NUM_KEYS];

// Store the indices of the advanced keys bind to each key. If no advanced key
// is bind to a key, the index is 0. Otherwise, the index is added by 1.
static uint8_t advanced_key_indices[NUM_LAYERS][NUM_KEYS];
// Same as `active_keycodes` but for advanced keys
static uint8_t active_advanced_keys[NUM_KEYS];

void layout_init(void) { layout_load_advanced_keys(); }

void layout_load_advanced_keys(void) {
  advanced_key_init();

  memset(advanced_key_indices, 0, sizeof(advanced_key_indices));
  for (uint32_t i = 0; i < NUM_ADVANCED_KEYS; i++) {
    const advanced_key_t *ak = &CURRENT_PROFILE.advanced_keys[i];

    if (ak->type == AK_TYPE_NONE || ak->layer >= NUM_LAYERS ||
        ak->key >= NUM_KEYS)
      continue;

    advanced_key_indices[ak->layer][ak->key] = i + 1;
    if (ak->type == AK_TYPE_NULL_BIND && ak->null_bind.secondary_key < NUM_KEYS)
      // Null Bind advanced keys also have a secondary key
      advanced_key_indices[ak->layer][ak->null_bind.secondary_key] = i + 1;
  }
}

void layout_task(void) {
  static advanced_key_event_t ak_event = {0};
  static uint32_t last_ak_tick = 0;

  const uint8_t current_layer = layout_get_current_layer();
  bool has_non_tap_hold_press = false;

  for (uint32_t i = 0; i < NUM_KEYS; i++) {
    const key_state_t *k = &key_matrix[i];
    const bool last_key_press = bitmap_get(key_press_states, i);

    if ((current_layer == 0) & eeconfig->options.xinput_enabled) {
      // XInput key only applies to layer 0. We process it first since the
      // subsequent key processing may be skipped due to the gamepad options.
      if (CURRENT_PROFILE.gamepad_buttons[i] != GP_BUTTON_NONE) {
        xinput_process(i);

        if (CURRENT_PROFILE.gamepad_options.gamepad_override)
          // If the key is mapped to a gamepad button, and the gamepad override
          // is enabled, we skip the key processing.
          continue;
      }

      if (!CURRENT_PROFILE.gamepad_options.keyboard_enabled)
        // If the keyboard is disabled for this profile, we skip the key
        // processing.
        continue;
    }

    if ((current_layer == 0) & bitmap_get(key_disabled, i))
      // Only keys in layer 0 can be disabled.
      continue;

    if (k->is_pressed & !last_key_press) {
      // Key press event
      const uint8_t keycode = layout_get_keycode(current_layer, i);
      const uint8_t ak_index = advanced_key_indices[current_layer][i];

      if (ak_index) {
        active_advanced_keys[i] = ak_index;
        ak_event = (advanced_key_event_t){
            .type = AK_EVENT_TYPE_PRESS,
            .key = i,
            .keycode = keycode,
            .ak_index = ak_index - 1,
        };
        advanced_key_process(&ak_event);
        has_non_tap_hold_press |=
            (CURRENT_PROFILE.advanced_keys[ak_index - 1].type !=
             AK_TYPE_TAP_HOLD);
      } else {
        active_keycodes[i] = keycode;
        layout_register(i, keycode);
        has_non_tap_hold_press |= (keycode != KC_NO);
      }
    } else if (!k->is_pressed & last_key_press) {
      // Key release event
      const uint8_t keycode = active_keycodes[i];
      const uint8_t ak_index = active_advanced_keys[i];

      if (ak_index) {
        active_advanced_keys[i] = 0;
        ak_event = (advanced_key_event_t){
            .type = AK_EVENT_TYPE_RELEASE,
            .key = i,
            .keycode = keycode,
            .ak_index = ak_index - 1,
        };
        advanced_key_process(&ak_event);
      } else {
        active_keycodes[i] = KC_NO;
        layout_unregister(i, keycode);
      }
    } else if (k->is_pressed) {
      // Key hold event
      const uint8_t keycode = active_keycodes[i];
      const uint8_t ak_index = active_advanced_keys[i];

      if (ak_index) {
        ak_event = (advanced_key_event_t){
            .type = AK_EVENT_TYPE_HOLD,
            .key = i,
            .keycode = keycode,
            .ak_index = ak_index - 1,
        };
        advanced_key_process(&ak_event);
      }
    }

    // Finally, update the key state
    bitmap_set(key_press_states, i, k->is_pressed);
  }

  if (has_non_tap_hold_press || timer_elapsed(last_ak_tick) > 0) {
    // We only need to tick the advanced keys every 1ms, or when there is a
    // non-Tap-Hold key press event since these are the only cases that
    // the advanced keys might perform an action.
    advanced_key_tick(has_non_tap_hold_press);
    last_ak_tick = timer_read();
  }

  if (should_send_reports) {
    hid_send_reports();
    should_send_reports = false;
  }

  // Process deferred actions for the next matrix scan
  deferred_action_process();
}

/**
 * @brief Set the current profile
 *
 * This function also refreshes the advanced keys, and saves the last
 * non-default profile for profile swapping.
 *
 * @param profile Profile index
 *
 * @return true if successful, false otherwise
 */
static bool layout_set_profile(uint8_t profile) {
  if (profile >= NUM_PROFILES)
    return false;

  advanced_key_clear();
  bool status = EECONFIG_WRITE(current_profile, &profile);
  if (status && profile != 0)
    status = EECONFIG_WRITE(last_non_default_profile, &profile);
  layout_load_advanced_keys();
#if defined(PROFILE_ACTIVE_KEY_MATRIX)
  // A different physical-layout profile enables a different Hall-sensor set.
  // Establish fresh rest values before accepting events from those sensors.
  if (status)
    matrix_recalibrate(false);
#endif

  return status;
}

void layout_register(uint8_t key, uint8_t keycode) {
  if (keycode == KC_NO)
    return;

  switch (keycode) {
  case HID_KEYCODE_RANGE:
    hid_keycode_add(keycode);
    should_send_reports = true;
    break;

  case MOMENTARY_LAYER_RANGE:
    layout_layer_on(MO_GET_LAYER(keycode));
    break;

  case PROFILE_RANGE:
    layout_set_profile(PF_GET_PROFILE(keycode));
    break;

  case SP_KEY_LOCK:
    bitmap_toggle(key_disabled, key);
    break;

  case SP_LAYER_LOCK:
    layout_layer_lock();
    break;

  case SP_PROFILE_SWAP:
    layout_set_profile(
        eeconfig->current_profile ? 0 : eeconfig->last_non_default_profile);
    break;

  case SP_PROFILE_NEXT:
    layout_set_profile((eeconfig->current_profile + 1) % NUM_PROFILES);
    break;

  case SP_BOOT:
    board_enter_bootloader();
    break;

  default:
    break;
  }
}

void layout_unregister(uint8_t key, uint8_t keycode) {
  if (keycode == KC_NO)
    return;

  switch (keycode) {
  case HID_KEYCODE_RANGE:
    hid_keycode_remove(keycode);
    should_send_reports = true;
    break;

  case MOMENTARY_LAYER_RANGE:
    layout_layer_off(MO_GET_LAYER(keycode));
    break;

  default:
    break;
  }
}
