Mokeded/Symm60HE/firmware/libhmk/include/common.h

/*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
 * You should have received a copy of the GNU General Public License along with
 * this program. If not, see <https://www.gnu.org/licenses/>.
 */

#pragma once

//--------------------------------------------------------------------+
// Firmware Version
//--------------------------------------------------------------------+

#if !defined(FIRMWARE_VERSION)
#define FIRMWARE_VERSION 0x0108
#endif

//--------------------------------------------------------------------+
// Common Headers
//--------------------------------------------------------------------+

#include <stdbool.h>
#include <stddef.h>
#include <stdint.h>
#include <stdlib.h>
#include <string.h>

#if defined(__has_include)
#if __has_include("config.h")
// Include additional configuration if available
#include "config.h"
#endif
#endif

#if defined(__has_include)
#if __has_include("board_def.h")
// Include board-specific definitions if available
#include "board_def.h"
#endif
#endif

//--------------------------------------------------------------------+
// Common Macros
//--------------------------------------------------------------------+

#define M_ARRAY_SIZE(arr) (sizeof(arr) / sizeof(arr[0]))
#define M_MIN(a, b) ((a) < (b) ? (a) : (b))
#define M_MAX(a, b) ((a) > (b) ? (a) : (b))
#define M_DIV_CEIL(n, d) (((n) + (d) - 1) / (d))
#define M_BIT(n) (1UL << (n))
#define M_IS_POWER_OF_TWO(n) (((n) != 0) && (((n) & ((n) - 1)) == 0))
#define M_HEX(n) ((n) < 10 ? '0' + (n) : 'A' - 10 + (n))

//--------------------------------------------------------------------+
// Keyboard Configuration
//--------------------------------------------------------------------+

#if !defined(NUM_PROFILES)
#error "NUM_PROFILES is not defined"
#endif

_Static_assert(1 <= NUM_PROFILES && NUM_PROFILES <= 8,
               "NUM_PROFILES must be between 1 and 16");

#if !defined(NUM_LAYERS)
#error "NUM_LAYERS is not defined"
#endif

_Static_assert(1 <= NUM_LAYERS && NUM_LAYERS <= 8,
               "NUM_LAYERS must be between 1 and 8");

#if !defined(NUM_KEYS)
#error "NUM_KEYS is not defined"
#endif

_Static_assert(1 <= NUM_KEYS && NUM_KEYS <= 256,
               "NUM_KEYS must be between 1 and 256");

#if !defined(NUM_ADVANCED_KEYS)
#error "NUM_ADVANCED_KEYS is not defined"
#endif

_Static_assert(1 <= NUM_ADVANCED_KEYS && NUM_ADVANCED_KEYS <= 64,
               "NUM_ADVANCED_KEYS must be between 1 and 64");

#if !defined(NUM_DYNAMIC_KEYSTROKE_MAX_BINDINGS)
#error "NUM_DYNAMIC_KEYSTROKE_MAX_BINDINGS is not defined"
#endif

_Static_assert(4 <= NUM_DYNAMIC_KEYSTROKE_MAX_BINDINGS &&
                   NUM_DYNAMIC_KEYSTROKE_MAX_BINDINGS <= 64,
               "NUM_DYNAMIC_KEYSTROKE_MAX_BINDINGS must be between 4 and 64");

#if !defined(NUM_MACRO_NODES)
#error "NUM_MACRO_NODES is not defined"
#endif

_Static_assert(1 <= NUM_MACRO_NODES && NUM_MACRO_NODES <= 255,
               "NUM_MACRO_NODES must be between 1 and 255");

//--------------------------------------------------------------------+
// Keyboard Types
//--------------------------------------------------------------------+

// Actuation configuration for a key. If `rt_down` is non-zero, Rapid Trigger is
// enabled. If `rt_up` is non-zero, both `rt_down` and `rt_up` are used to
// configure the Rapid Trigger press and release sensitivity, respectively.
typedef struct __attribute__((packed)) {
  // Actuation point (0-255)
  uint8_t actuation_point;
  // Rapid Trigger press sensitivity (0-255)
  uint8_t rt_down;
  // Rapid Trigger release sensitivity (0-255)
  uint8_t rt_up;
  // Whether Continuous Rapid Trigger is enabled
  bool continuous;
} actuation_t;

// Advanced key types
typedef enum {
  AK_TYPE_NONE = 0,
  AK_TYPE_NULL_BIND,
  AK_TYPE_DYNAMIC_KEYSTROKE,
  AK_TYPE_TAP_HOLD,
  AK_TYPE_TOGGLE,
  AK_TYPE_MACRO,
  AK_TYPE_COUNT,
} ak_type_t;

// Null Bind resolution behavior when both primary and secondary keys are
// pressed at the same time
typedef enum {
  // Prioritize the last pressed key
  NB_BEHAVIOR_LAST = 0,
  // Prioritize the primary key
  NB_BEHAVIOR_PRIMARY,
  // Prioritize the secondary key
  NB_BEHAVIOR_SECONDARY,
  // Release both keys
  NB_BEHAVIOR_NEUTRAL,
  // Prioritize the key that is pressed further
  NB_BEHAVIOR_DISTANCE,
} nb_behavior_t;

// Null Bind configuration
typedef struct __attribute__((packed)) {
  uint8_t secondary_key;
  uint8_t behavior;
  // Bottom-out point (0-255). If non-zero, both keys will be registered if both
  // of them are pressed past this point, regardless of the behavior.
  uint8_t bottom_out_point;
} null_bind_t;

// Dynamic Keystroke actions for each part of the keystroke
typedef enum {
  DKS_ACTION_HOLD = 0,
  DKS_ACTION_PRESS,
  DKS_ACTION_RELEASE,
  DKS_ACTION_TAP,
} dks_action_t;

// Dynamic Keystroke configuration
typedef struct __attribute__((packed)) {
  // Bind up to `NUM_DYNAMIC_KEYSTROKE_MAX_BINDINGS` keycodes
  uint8_t keycodes[NUM_DYNAMIC_KEYSTROKE_MAX_BINDINGS];
  // For each keycode, bind up to 4 actions for each part of the keystroke
  // Bit 0-1: Action for key press
  // Bit 2-3: Action for key bottom-out
  // Bit 4-5: Action for key release from bottom-out
  // Bit 6-7: Action for key release
  uint8_t bitmap[NUM_DYNAMIC_KEYSTROKE_MAX_BINDINGS];
  // Bottom-out point (0-255)
  uint8_t bottom_out_point;
} dynamic_keystroke_t;

// Tap-Hold configuration
typedef struct __attribute__((packed)) {
  uint8_t tap_keycode;
  uint8_t hold_keycode;
  // Tapping term in milliseconds
  uint16_t tapping_term;
  // Whether to immediately register the hold action if another non-Tap-Hold key
  // is pressed, regardless of the tapping term
  bool hold_on_other_key_press;
} tap_hold_t;

// Toggle configuration
typedef struct __attribute__((packed)) {
  uint8_t keycode;
  // Tapping term in milliseconds
  uint16_t tapping_term;
} toggle_t;

// Macro action
typedef enum {
  MACRO_ACTION_NONE = 0,
  MACRO_ACTION_PRESS,
  MACRO_ACTION_TAP,
  MACRO_ACTION_RELEASE,
  MACRO_ACTION_COUNT,
} macro_action_t;

typedef uint8_t macro_node_id_t;

#define MACRO_NODE_NONE UINT8_MAX

typedef struct __attribute__((packed)) {
  uint8_t keycode;
  uint8_t action : 3;
  // Delay in milliseconds
  uint16_t delay : 13;
  macro_node_id_t next;
} macro_node_t;

_Static_assert(MACRO_ACTION_COUNT < 8,
               "MACRO_ACTION_COUNT must be less than 8");

// Macro configuration
typedef struct __attribute__((packed)) {
  // The first macro node in the linked list
  macro_node_id_t head;
} macro_t;

// Advanced key configuration
typedef struct __attribute__((packed)) {
  uint8_t layer;
  uint8_t key;
  uint8_t type;
  union __attribute__((packed)) {
    null_bind_t null_bind;
    dynamic_keystroke_t dynamic_keystroke;
    tap_hold_t tap_hold;
    toggle_t toggle;
    macro_t macro;
  };
} advanced_key_t;

// Gamepad buttons
typedef enum {
  GP_BUTTON_NONE = 0,

  // Digital buttons
  GP_BUTTON_A,
  GP_BUTTON_B,
  GP_BUTTON_X,
  GP_BUTTON_Y,
  GP_BUTTON_UP,
  GP_BUTTON_DOWN,
  GP_BUTTON_LEFT,
  GP_BUTTON_RIGHT,
  GP_BUTTON_START,
  GP_BUTTON_BACK,
  GP_BUTTON_HOME,
  GP_BUTTON_LS,
  GP_BUTTON_RS,
  GP_BUTTON_LB,
  GP_BUTTON_RB,

  // Analog buttons
  GP_BUTTON_LS_UP,
  GP_BUTTON_LS_DOWN,
  GP_BUTTON_LS_LEFT,
  GP_BUTTON_LS_RIGHT,
  GP_BUTTON_RS_UP,
  GP_BUTTON_RS_DOWN,
  GP_BUTTON_RS_LEFT,
  GP_BUTTON_RS_RIGHT,
  GP_BUTTON_LT,
  GP_BUTTON_RT,
} gamepad_button_t;

// Gamepad options configuration
typedef struct __attribute__((packed)) {
  // 4 points that define the analog curve, representing the relationship
  // between the key position and the gamepad analog value
  uint8_t analog_curve[4][2];
  union __attribute__((packed)) {
    struct __attribute__((packed)) {
      // Whether to enable the layout processing for this profile
      bool keyboard_enabled : 1;
      // Whether the layout module should process the underlying key if the key
      // is mapped to a gamepad button
      bool gamepad_override : 1;
      // Whether the joystick output is square-shaped instead of circular
      bool square_joystick : 1;
      // Whether to use the maximum value of opposite axes for the joystick
      // output instead of combining them
      bool snappy_joystick : 1;
      // Reserved bits for future use
      uint8_t reserved : 4;
    };
    uint8_t options;
  };
} gamepad_options_t;
