Mokeded/Symm60HE/firmware/libhmk/scripts/make.py

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
import utils
from drivers import *
from schema.keyboard import KeyboardUSBPort

Import("env")

keyboard = env["PIOENV"]

# Load JSON files and driver. We assume that they have been validated in `get_deps.py`.
kb_json = utils.get_kb_json(keyboard)
driver = utils.get_driver(keyboard)
driver_name = kb_json.hardware.driver

# Add source filter for driver source files
env.Append(SRC_FILTER=["-<hardware/>", f"+<hardware/{driver_name}/>"])

# Build Flags
build_flags = utils.CompilerFlags()

# Include headers. We prioritize including driver and keyboard headers.
build_flags.include(f"hardware/{driver_name}")
build_flags.include(f"keyboards/{keyboard}")
build_flags.include("include")

# Bootloader Configuration
build_flags.define("BOOTLOADER_ADDR", driver.metadata.bootloader.address)
build_flags.define("BOOTLOADER_MAGIC", driver.metadata.bootloader.magic)

# Flash Configuration
flash_size = driver.metadata.flash.get_flash_size()
flash_num_sectors = driver.metadata.flash.get_num_sectors()
build_flags.define("FLASH_SIZE", flash_size)
build_flags.linker_defsym("FLASH_SIZE", flash_size)
build_flags.define("FLASH_NUM_SECTORS", flash_num_sectors)
build_flags.define("FLASH_EMPTY_VAL", driver.metadata.flash.empty_value)

match driver.metadata.flash.sector_sizes:
    case NonUniformSectors(sizes):
        build_flags.define("FLASH_SECTOR_SIZES", utils.to_c_array(sizes))
    case UniformSectors(size, _):
        build_flags.define("FLASH_SECTOR_SIZE", size)

# TinyUSB Configuration
build_flags.define("CFG_TUSB_MCU", f"OPT_MCU_{driver.tinyusb.mcu.upper()}")

# Clock Configuration
build_flags.define("BOARD_HSE_VALUE", kb_json.hardware.hse_value)
build_flags.define("HSE_VALUE", kb_json.hardware.hse_value)
if kb_json.firmware_version is not None:
    build_flags.define("FIRMWARE_VERSION", kb_json.firmware_version)

# USB Configuration
if kb_json.usb.port == KeyboardUSBPort.FULL_SPEED:
    build_flags.define("BOARD_USB_FS")
else:
    build_flags.define("BOARD_USB_HS")
build_flags.define("USB_MANUFACTURER_NAME", f'"{kb_json.manufacturer}"')
build_flags.define("USB_PRODUCT_NAME", f'"{kb_json.name}"')
build_flags.define("USB_VENDOR_ID", kb_json.usb.vid)
build_flags.define("USB_PRODUCT_ID", kb_json.usb.pid)

# Analog Configuration
build_flags.define("ADC_NUM_CHANNELS", len(driver.metadata.adc.input_pins))
build_flags.define("ADC_RESOLUTION", utils.get_adc_resolution(kb_json, driver))

if kb_json.analog.invert_adc:
    build_flags.define("MATRIX_INVERT_ADC_VALUES")

if kb_json.analog.delay is not None:
    build_flags.define("ADC_SAMPLE_DELAY", kb_json.analog.delay)

# Raw ADC Input Configuration
if kb_json.analog.raw is not None:
    raw = kb_json.analog.raw

    build_flags.define("ADC_NUM_RAW_INPUTS", len(raw.input))
    build_flags.define(
        "ADC_RAW_INPUT_CHANNELS",
        utils.to_c_array(driver.metadata.adc.to_adc_inputs(raw.input)),
    )
    build_flags.define("ADC_RAW_INPUT_VECTOR", utils.to_c_array(raw.vector))

# Analog Multiplexer ADC Input Configuration
if kb_json.analog.mux is not None:
    mux = kb_json.analog.mux

    build_flags.define("ADC_NUM_MUX_INPUTS", len(mux.input))
    build_flags.define(
        "ADC_MUX_INPUT_CHANNELS",
        utils.to_c_array(driver.metadata.adc.to_adc_inputs(mux.input)),
    )
    build_flags.define("ADC_NUM_MUX_SELECT_PINS", len(mux.select))

    ports, pin_nums = driver.metadata.adc.to_gpio_array(mux.select)
    build_flags.define("ADC_MUX_SELECT_PORTS", utils.to_c_array(ports))
    build_flags.define("ADC_MUX_SELECT_PINS", utils.to_c_array(pin_nums))

    build_flags.define(
        "ADC_MUX_INPUT_MATRIX", utils.to_c_array(list(map(list, zip(*mux.matrix))))
    )

# Calibration Configuration
build_flags.define(
    "DEFAULT_CALIBRATION", utils.to_c_struct(kb_json.calibration.model_dump())
)

# Addressable RGB Configuration
if kb_json.rgb is not None:
    rgb = kb_json.rgb
    rgb_pins = [output.pin for output in rgb.outputs]
    rgb_ports, rgb_pin_nums = driver.metadata.adc.to_gpio_array(rgb_pins)
    if len(set(rgb_ports)) != 1:
        raise ValueError("RGB outputs must share one GPIO port")

    build_flags.define("RGB_ENABLE")
    build_flags.define("RGB_NUM_OUTPUTS", len(rgb.outputs))
    build_flags.define("RGB_OUTPUT_PORT", rgb_ports[0])
    build_flags.define("RGB_OUTPUT_PORT_CLOCK", f"CRM_{rgb_ports[0]}_PERIPH_CLOCK")
    build_flags.define("RGB_OUTPUT_PINS", utils.to_c_array(rgb_pin_nums))
    build_flags.define(
        "RGB_LED_COUNTS",
        utils.to_c_array([output.led_count for output in rgb.outputs]),
    )
    build_flags.define(
        "RGB_MAX_LED_COUNT", max(output.led_count for output in rgb.outputs)
    )
    build_flags.define("RGB_CURRENT_LIMIT_MA", rgb.current_limit_ma)
    build_flags.define("RGB_CHANNEL_CURRENT_MA", rgb.channel_current_ma)
    build_flags.define("RGB_REFRESH_HZ", rgb.refresh_hz)

# Wear leveling configuration
wear_leveling = kb_json.wear_leveling
wl_virtual_size = (wear_leveling and wear_leveling.virtual_size) or 8192
wl_write_log_size = (wear_leveling and wear_leveling.write_log_size) or 65536
wl_backing_store_size = wl_virtual_size + wl_write_log_size

build_flags.define("WL_VIRTUAL_SIZE", wl_virtual_size)
build_flags.define("WL_WRITE_LOG_SIZE", wl_write_log_size)

# Reserve flash for wear leveling (round up to whole sectors from the end)
wl_base_address = flash_size - driver.metadata.flash.round_up_to_flash_sectors(
    wl_backing_store_size
)
build_flags.define("WL_BASE_ADDRESS", wl_base_address)
build_flags.linker_defsym("WL_BASE_ADDRESS", wl_base_address)

# Keyboard Configuration
kb = kb_json.keyboard
build_flags.define("NUM_PROFILES", kb.num_profiles)
build_flags.define("NUM_LAYERS", kb.num_layers)
build_flags.define("NUM_KEYS", kb.num_keys)
build_flags.define("NUM_ADVANCED_KEYS", kb.num_advanced_keys)
if kb.active_key_masks is not None:
    build_flags.define(
        "PROFILE_ACTIVE_KEY_MATRIX", utils.to_c_array(kb.active_key_masks)
    )
build_flags.define(
    "NUM_DYNAMIC_KEYSTROKE_MAX_BINDINGS", kb.num_dynamic_keystroke_max_bindings
)
build_flags.define("NUM_MACRO_NODES", kb.num_macro_nodes)

# Default Keymaps (per profile)
default_keymaps = utils.resolve_default_keymaps(kb_json)
build_flags.define("DEFAULT_KEYMAPS", utils.to_c_array(default_keymaps))

# Actuation Configuration
if kb_json.actuation is not None:
    actuation = kb_json.actuation
    if actuation.actuation_point is not None:
        build_flags.define("ACTUATION_POINT", actuation.actuation_point)

# Add source build flags
env.Append(BUILD_FLAGS=build_flags.get_flags())
