Mokeded/Symm60HE/firmware/libhmk/scripts/schema/keyboard.py

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
from enum import Enum
from pydantic import BaseModel, Field, NonNegativeInt, PositiveFloat, PositiveInt


class KeyboardUSBPort(str, Enum):
    FULL_SPEED = "fs"
    HIGH_SPEED = "hs"


# USB Configuration
class KeyboardUSB(BaseModel):
    # USB Vendor ID
    vid: str = Field(pattern=r"^0x[0-9A-Fa-f]{4}$")
    # USB Product ID
    pid: str = Field(pattern=r"^0x[0-9A-Fa-f]{4}$")
    port: KeyboardUSBPort


# Keyboard Configuration
class KeyboardKeyboard(BaseModel):
    num_profiles: int = Field(ge=1, le=8)
    num_layers: int = Field(ge=1, le=8)
    num_keys: int = Field(ge=1, le=256)
    num_advanced_keys: int = Field(ge=1, le=64)
    # Maximum number of Dynamic Keystroke bindings per key. Higher values may require higher storage sizes.
    num_dynamic_keystroke_max_bindings: int = Field(ge=4, le=64, default=4)
    num_macro_nodes: int = Field(ge=1, le=255, default=128)
    # Optional compile-time profile descriptions and Hall-channel masks. A zero
    # mask entry prevents that key from being calibrated or scanned while the
    # corresponding profile is active.
    profile_names: list[str] | None = None
    active_key_masks: list[list[int]] | None = None


# Hardware Configuration
class KeyboardHardware(BaseModel):
    # High-speed external oscillator value in Hz
    hse_value: PositiveInt
    # Keyboard driver name
    driver: str


class KeyboardRGBOutput(BaseModel):
    # Human-readable output name and MCU GPIO pin for one addressable LED chain.
    name: str
    pin: str
    led_count: int = Field(ge=1, le=256)


class KeyboardRGB(BaseModel):
    # Multiple chains are transmitted in parallel when they share one GPIO port.
    outputs: list[KeyboardRGBOutput] = Field(min_length=1, max_length=8)
    current_limit_ma: int = Field(ge=50, le=5000)
    channel_current_ma: int = Field(ge=1, le=50, default=12)
    refresh_hz: int = Field(ge=1, le=60, default=30)


# Raw ADC input configuration
class KeyboardAnalogRaw(BaseModel):
    # Array of raw ADC input channels. If a string is provided, it is used as the GPIO pin name
    input: list[NonNegativeInt | str]
    # Array of key index mappings for the raw ADC inputs
    vector: list[NonNegativeInt]


# Analog Multiplexer ADC input configuration
class KeyboardAnalogMux(BaseModel):
    # Array of GPIO pin names for the multiplexer select lines
    select: list[str]
    # Array of ADC input channels for the multiplexers. If a string is provided, it is used as the GPIO pin name
    input: list[NonNegativeInt | str]
    # Mapping from multiplexers to ADC input channels
    matrix: list[list[NonNegativeInt]]


# Analog Configuration
class KeyboardAnalog(BaseModel):
    # ADC resolution for this keyboard. A higher value means higher accuracy but slower matrix scans. Default to the maximum resolution supported by the MCU if not provided.
    adc_resolution: PositiveInt | None = None
    # Set to true if the ADC value is inversely proportional to the travel distance of the keys
    invert_adc: bool = False
    # Delay in microseconds between ADC scans
    delay: int | None = None
    raw: KeyboardAnalogRaw | None = None
    mux: KeyboardAnalogMux | None = None


# Calibration Configuration
class KeyboardCalibration(BaseModel):
    # See `include/lib/eeconfig.h`
    initial_rest_value: NonNegativeInt
    # See `include/lib/eeconfig.h`
    initial_bottom_out_threshold: NonNegativeInt


# Wear leveling Configuration
class KeyboardWearLeveling(BaseModel):
    # Size of the virtual persistent storage in bytes. There must be enough RAM of this size to hold the entire virtual storage.
    virtual_size: int = Field(ge=1, le=16384)
    # Size of the write log in bytes
    write_log_size: int = Field(ge=1, le=65536)


class KeyboardLayoutKey(BaseModel):
    key: NonNegativeInt
    w: PositiveFloat | None = None
    h: PositiveFloat | None = None
    x: float | None = None
    y: float | None = None
    # Option key and value pairs for the corresponding labels
    option: tuple[int, int] | None = None


# Keyboard Layout
class KeyboardLayout(BaseModel):
    # Labels for each layout option. Use a string for a toggle option, or an array for a select option
    labels: list[str | list[str]] | None = None
    # Metadata for how the keyboard should be rendered in the web configurator
    keymap: list[list[KeyboardLayoutKey]]


# Actuation Configuration
class KeyboardActuation(BaseModel):
    # Default actuation point
    actuation_point: int = Field(ge=0, le=255)


# keyboard.json Schema
class Keyboard(BaseModel):
    name: str
    manufacturer: str
    maintainer: str
    firmware_version: str | None = Field(
        default=None, pattern=r"^0x[0-9A-Fa-f]{4}$"
    )
    usb: KeyboardUSB
    keyboard: KeyboardKeyboard
    hardware: KeyboardHardware
    rgb: KeyboardRGB | None = None
    analog: KeyboardAnalog
    calibration: KeyboardCalibration
    wear_leveling: KeyboardWearLeveling | None = None
    layout: KeyboardLayout
    # Default keymap
    keymap: list[list[str]] | None = None
    # Default keymaps for each profile. If not specified, the default keymap will be used for all profiles.
    keymaps: list[list[list[str]]] | None = None
    actuation: KeyboardActuation | None = None
