Mokeded/Symm60HE/firmware/libhmk/scripts/validate.py

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
import json
import os
import utils

Import("env")

keyboard = env["PIOENV"]

# Load driver (only for validation)
utils.get_driver(keyboard)

# Load JSON files and validate
kb_json = utils.get_kb_json(keyboard)

# Validate default keymaps
default_keymaps = utils.resolve_default_keymaps(kb_json)

if kb_json.keyboard.profile_names is not None:
    if len(kb_json.keyboard.profile_names) != kb_json.keyboard.num_profiles:
        raise ValueError("Expected one profile name per keyboard profile")

if kb_json.keyboard.active_key_masks is not None:
    masks = kb_json.keyboard.active_key_masks
    if len(masks) != kb_json.keyboard.num_profiles:
        raise ValueError("Expected one active-key mask per keyboard profile")
    if any(len(mask) != kb_json.keyboard.num_keys for mask in masks):
        raise ValueError("Each active-key mask must contain num_keys entries")
    if any(value not in (0, 1) for mask in masks for value in mask):
        raise ValueError("Active-key mask entries must be zero or one")
if len(default_keymaps) != kb_json.keyboard.num_profiles:
    raise ValueError(
        f"Expected default keymaps to have {kb_json.keyboard.num_profiles} profiles"
    )
for keymap in default_keymaps:
    if len(keymap) != kb_json.keyboard.num_layers:
        raise ValueError(
            f"Expected default keymaps to have {kb_json.keyboard.num_layers} layers"
        )
    for layer in keymap:
        if len(layer) != kb_json.keyboard.num_keys:
            raise ValueError(
                f"Expected default keymaps to have {kb_json.keyboard.num_keys} keys"
            )
